umbertoragone/usbc-rtl-sdr/images/img_3.jpg

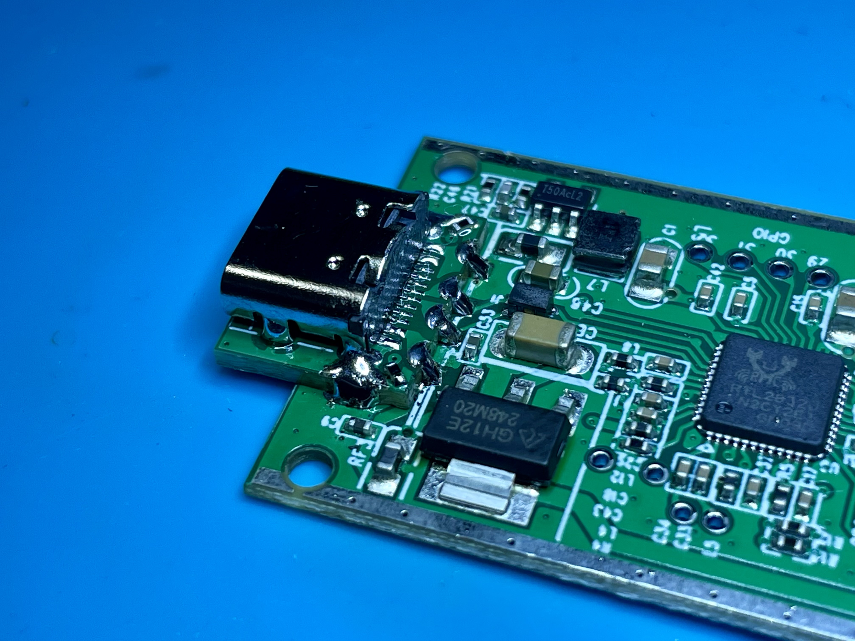
images/img_3.jpg
