umbertoragone/usbc-rtl-sdr/images/img_4.jpg

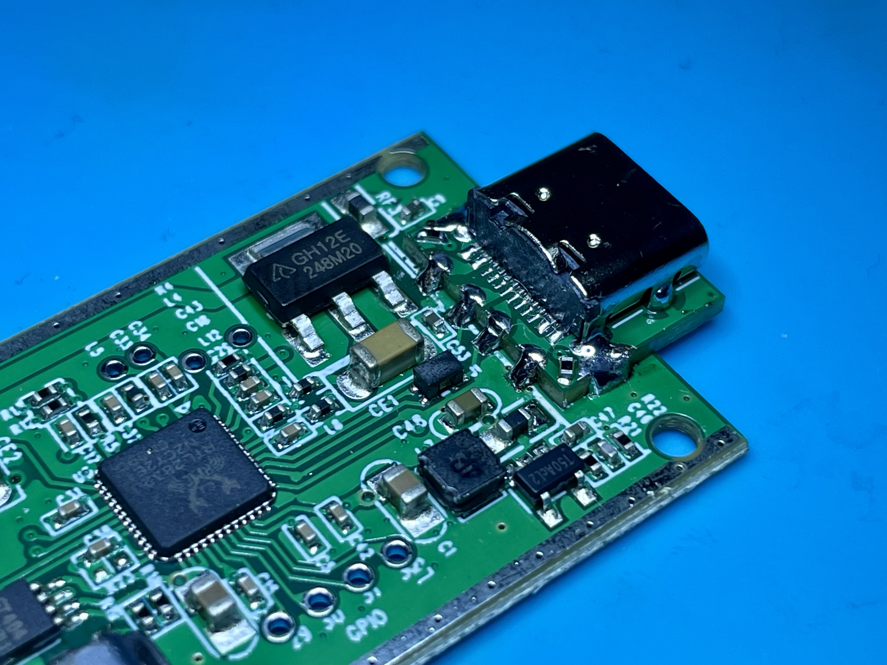
images/img_4.jpg
