umbertoragone/usbc-rtl-sdr/images/img_5.jpg

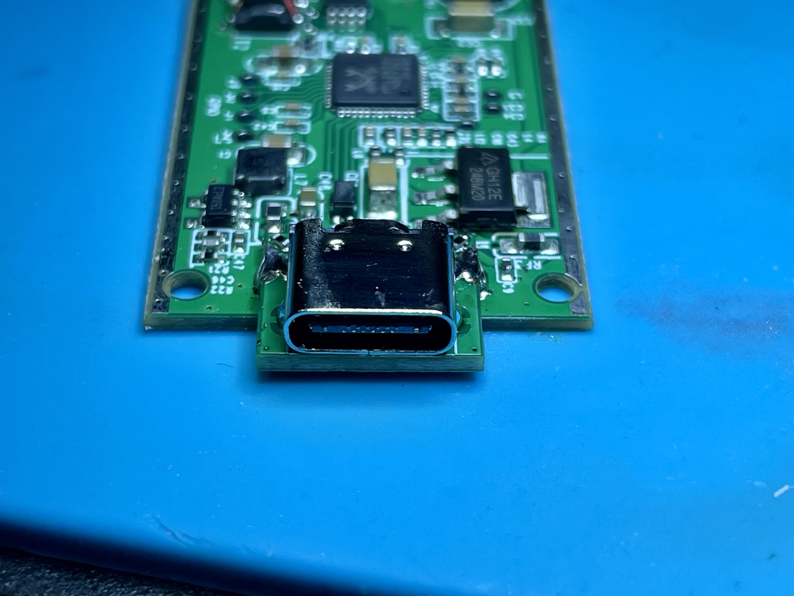
images/img_5.jpg
