umbertoragone/usbc-rtl-sdr/images/img_6.jpg

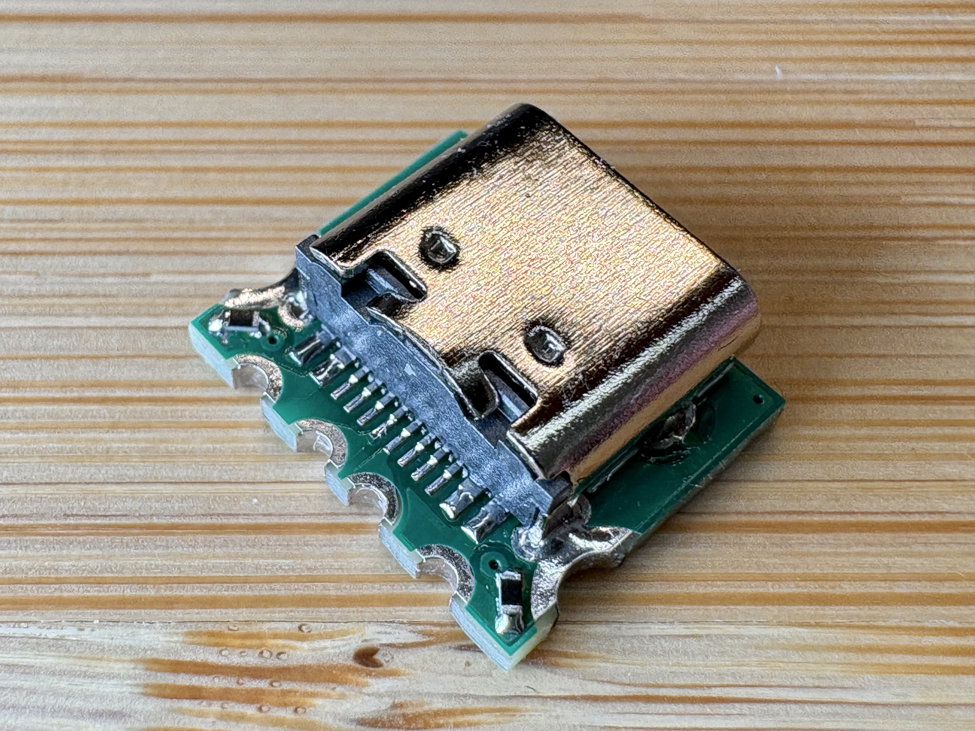
images/img_6.jpg
